MadsRudolph/Oscilloscope_Project/docs/Kicad/Spice_Models/TLV3501/TLV3501-PSpiceFiles/SCHEMATIC1/TLV3501_SIM/TLV3501_SIM.cir

** Profile: "SCHEMATIC1-TLV3501_SIM"  [ C:\Modeling\TLV3501\PSPICE\TLV3501-PSpiceFiles\SCHEMATIC1\TLV3501_SIM.sim ] 

** Creating circuit file "TLV3501_SIM.cir" 
** WARNING: THIS AUTOMATICALLY GENERATED FILE MAY BE OVERWRITTEN BY SUBSEQUENT SIMULATIONS

*Libraries: 
* Profile Libraries :
* Local Libraries :
.LIB "../../../tlv3501.lib" 
* From [PSPICE NETLIST] section of C:\SPB_DATA\cdssetup\OrCAD_PSpice\17.4.0\PSpice.ini file:
.lib "nom.lib" 

*Analysis directives: 
.TRAN  0 500ns 0 
.OPTIONS ADVCONV
.PROBE64 V(alias(*)) I(alias(*)) W(alias(*)) D(alias(*)) NOISE(alias(*)) 
.INC "..\SCHEMATIC1.net" 


.END
