MadsRudolph/Oscilloscope_Project/docs/LTspice/Projekt Filter Simulation.asc

C1: cap; 3.18n
C2: cap; 0.47n
C3: cap; 0.47n
C4: cap; 0.47n
C5: cap; 0.47n
R1: res; 6.49k
R2: res; 1000
R3: res; 6.49k
R4: res; 6.49k
R5: res; 6.49k
R6: res
U1: LT1713
U2: LT1013
U4: LT1013
V1: voltage; 5
V2: voltage; 3.3
V3: voltage; SINE(1 1 1000); AC 1 0
V4: voltage; -5
V5: voltage; 5
V6: voltage; -5
V_const: voltage; 1.65
V_saw: voltage; PULSE(0 3.3 0 0.0001 0 0 0.0001)
V_sin: voltage; SINE(1.65 1.65 1000)
V_Square: voltage; PULSE(0 3.3 0 0 0 0.0005 0.001)
V_tri: voltage; PULSE(0 3.3 0 1.28u 1.28u 0 0)
Named nets: V_tri, 0, V_Saw, PWM, V_Sin, V_Square, V_const, BODE
.tran 10m
