MadsRudolph/Oscilloscope_Project/docs/LTspice/Filter.asc

R1: res; 5
R2: res; 5
R3: res; 10
V1: voltage; 5
.tran 10
