MadsRudolph/Oscilloscope_Project/docs/Kicad/FilterDesign/Active_Filter.kicad_sch

## KiCad design docs/Kicad/FilterDesign/Active_Filter.kicad_sch (2025-06-14)

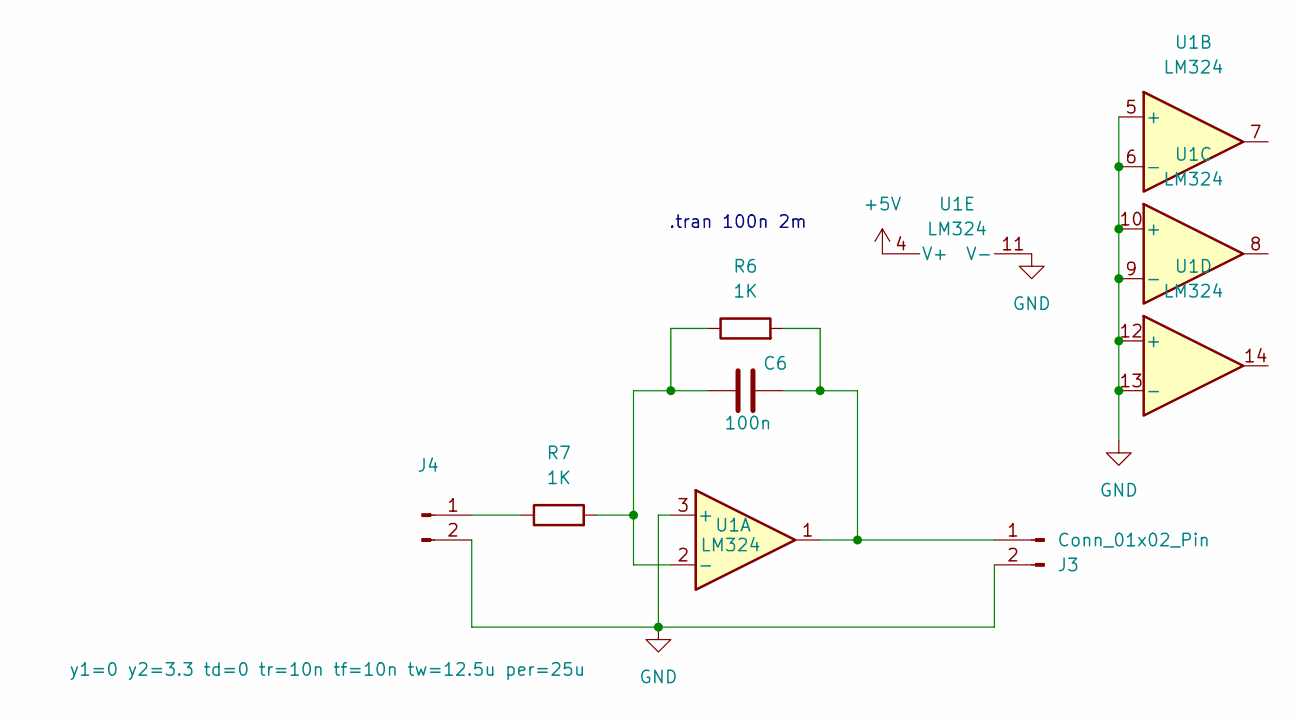
[picture p2: schematic Active_Filter.kicad_sch]

Parts:
C6: 100n
J3: Conn_01x02_Pin
J4: y1=0 y2=3.3 td=0 tr=10n tf=10n tw=12.5u per=25u
R6, R7: 1K
U1: LM324

Connections:
+5V: U1.4 (V+)
GND: J3.2, J4.2, U1.3 (+), U1.5 (+), U1.6 (-), U1.9 (-), U1.10 (+), U1.11 (V-), U1.12 (+), U1.13 (-)
unnamed: C6.1, R6.1, R7.2, U1.2 (-)
unnamed: C6.2, J3.1, R6.2, U1.1
unnamed: J4.1, R7.1

Notes on the sheet:
.tran 100n 2m
