MadsRudolph/Oscilloscope_Project/docs/Kicad/FilterDesign/Passive_filter.kicad_sch

## KiCad design docs/Kicad/FilterDesign/Passive_filter.kicad_sch (2025-06-16, an earlier design)

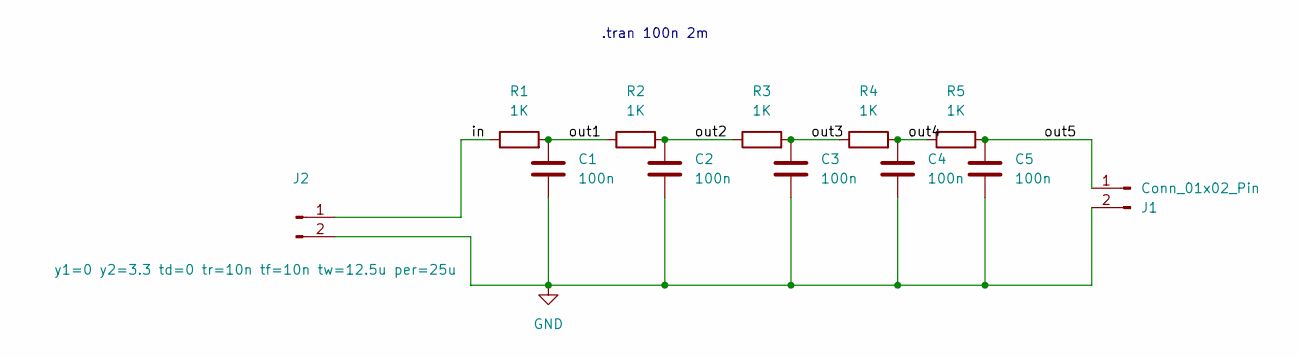
[picture p3: schematic Passive_filter.kicad_sch]

Parts:
C1, C2, C3, C4, C5: 100n
J1: Conn_01x02_Pin
J2: y1=0 y2=3.3 td=0 tr=10n tf=10n tw=12.5u per=25u
R1, R2, R3, R4, R5: 1K

Connections:
GND: C1.2, C2.2, C3.2, C4.2, C5.2, J1.2, J2.2
in: J2.1, R1.1
out1: C1.1, R1.2, R2.1
out2: C2.1, R2.2, R3.1
out3: C3.1, R3.2, R4.1
out4: C4.1, R4.2, R5.1
out5: C5.1, J1.1, R5.2

Notes on the sheet:
.tran 100n 2m
