MadsRudolph/Oscilloscope_Project/docs/Kicad/FilterDesign/Sallen-key topology low-pass.kicad_sch

## KiCad design docs/Kicad/FilterDesign/Sallen-key topology low-pass.kicad_sch (2025-06-19, an earlier design)

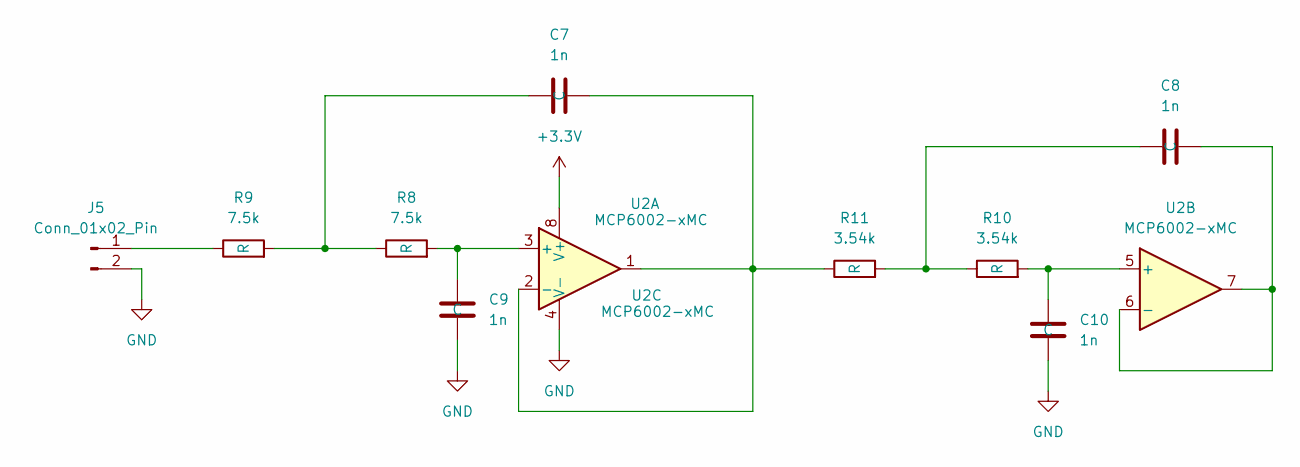
[picture p4: schematic Sallen-key topology low-pass.kicad_sch]

Parts:
C7, C8, C9, C10: 1n
J5: Conn_01x02_Pin
R8, R9: 7.5k
R10, R11: 3.54k
U2: MCP6002-xMC; DFN-8-1EP_3x2mm_P0.5mm_EP1.75x1.45mm

Connections:
+3.3V: U2.8 (V+)
GND: C9.2, C10.2, J5.2, U2.4 (V-), U2.9 (V-)
unnamed: C7.1, R8.1, R9.2
unnamed: C7.2, R11.1, U2.1, U2.2 (-)
unnamed: C8.1, R10.1, R11.2
unnamed: C8.2, U2.6 (-), U2.7
unnamed: C9.1, R8.2, U2.3 (+)
unnamed: C10.1, R10.2, U2.5 (+)
unnamed: J5.1, R9.1
