MadsRudolph/Oscilloscope_Project/docs/Kicad/FilterDesign/AktivtFilterSim/AktivtFilterSim.kicad_sch

## KiCad design docs/Kicad/FilterDesign/AktivtFilterSim/AktivtFilterSim.kicad_sch (2025-06-19, an earlier design)

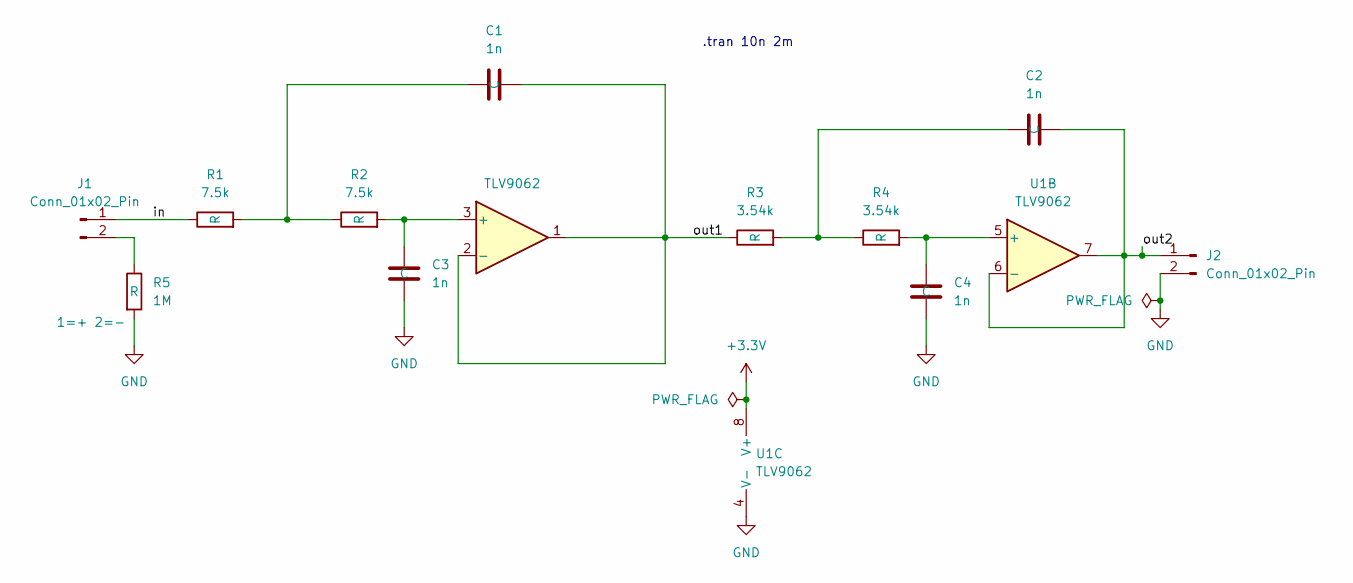
[picture p5: schematic AktivtFilterSim.kicad_sch]

Parts:
C1, C2, C3, C4: 1n
J1, J2: Conn_01x02_Pin
R1, R2: 7.5k
R3, R4: 3.54k
R5: 1M
U1: TLV9062

Connections:
+3.3V: U1.8 (V+)
GND: C3.2, C4.2, J2.2, R5.2, U1.4 (V-)
unnamed: C1.1, R1.2, R2.1
unnamed: C2.1, R3.2, R4.1
unnamed: C3.1, R2.2, U1.3 (+)
unnamed: C4.1, R4.2, U1.5 (+)
unnamed: J1.2, R5.1
in: J1.1, R1.1
out1: C1.2, R3.1, U1.1, U1.2 (-)
out2: C2.2, J2.1, U1.6 (-), U1.7

Notes on the sheet:
.tran 10n 2m
