MadsRudolph/Oscilloscope_Project/docs/Kicad/FilterDesign/Comparator/Comparator.kicad_sch

## KiCad design docs/Kicad/FilterDesign/Comparator/Comparator.kicad_sch (2025-06-19)

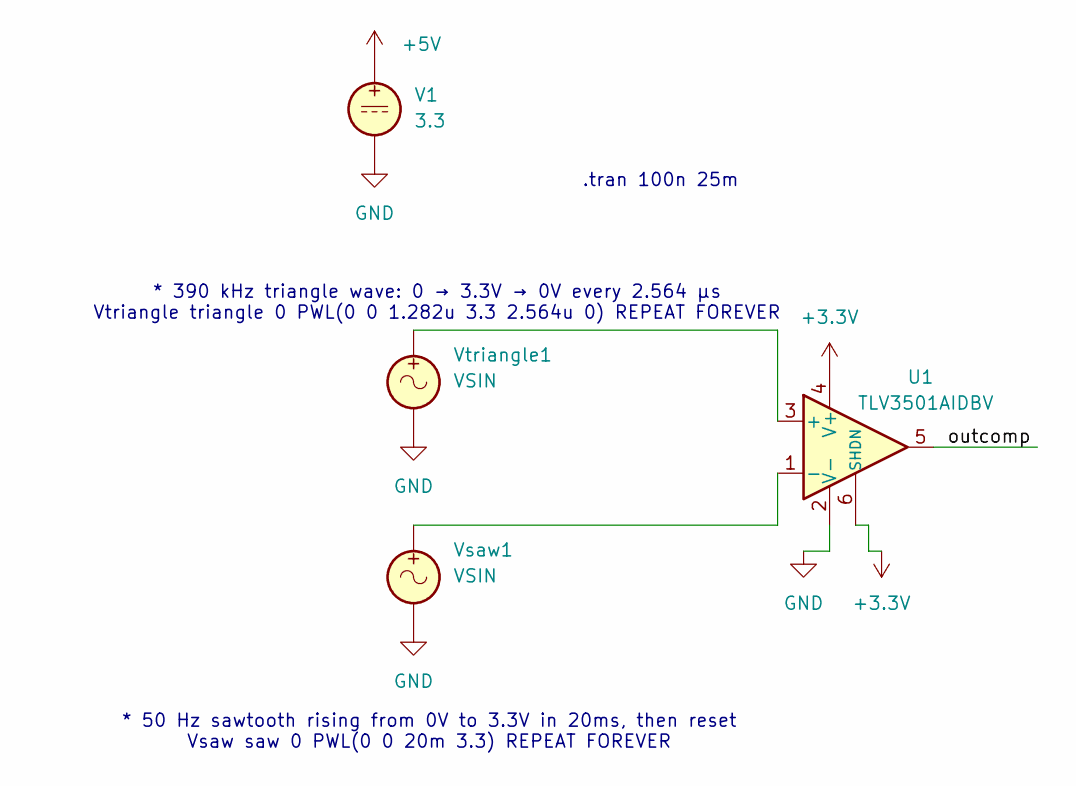
[picture p6: schematic Comparator.kicad_sch]

Parts:
U1: TLV3501AIDBV; SOT-23-6
V1: 3.3
Vsaw1: VSIN
Vtriangle1: VSIN

Connections:
+3.3V: U1.4 (V+), U1.6 (SHDN)
+5V: V1.1
GND: U1.2 (V-), V1.2, Vsaw1.2, Vtriangle1.2
unnamed: U1.1 (-), Vsaw1.1
unnamed: U1.3 (+), Vtriangle1.1
outcomp: U1.5

Notes on the sheet:
.tran 100n 25m
* 390 kHz triangle wave: 0 → 3.3V → 0V every 2.564 µs Vtriangle triangle 0 PWL(0 0 1.282u 3.3 2.564u 0) REPEAT FOREVER
* 50 Hz sawtooth rising from 0V to 3.3V in 20ms, then reset Vsaw saw 0 PWL(0 0 20m 3.3) REPEAT FOREVER
