MadsRudolph/Oscilloscope_Project/docs/Kicad/FilterDesign/FinalFilter/FinalFilter.kicad_sch

## KiCad design docs/Kicad/FilterDesign/FinalFilter/FinalFilter.kicad_sch (2025-06-23)

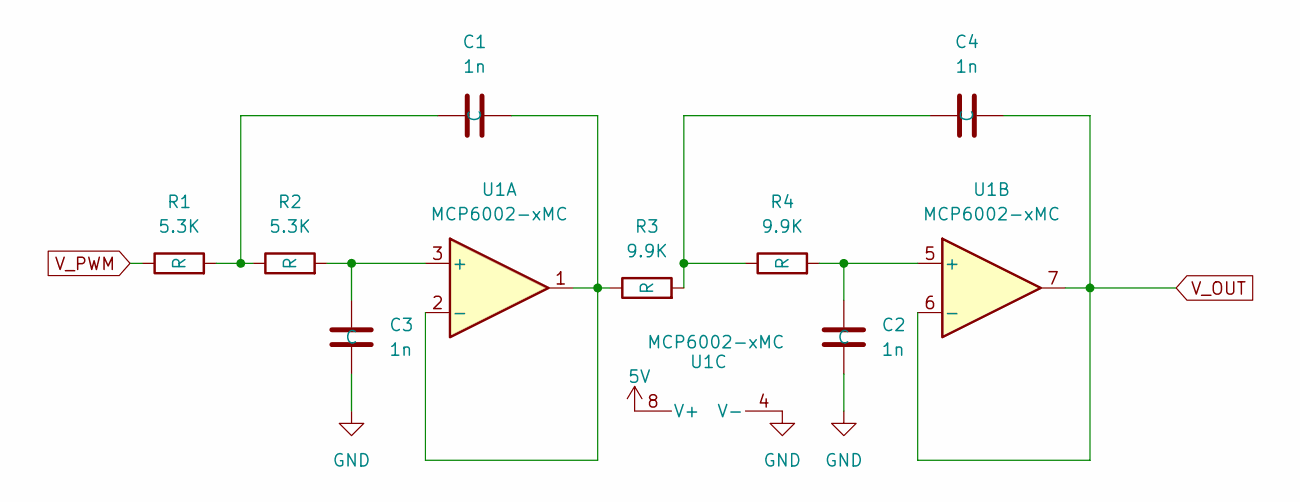
[picture p7: schematic FinalFilter.kicad_sch]

Parts:
C1, C2, C3, C4: 1n
R1, R2: 5.3K
R3, R4: 9.9K
U1: MCP6002-xMC; DFN-8-1EP_3x2mm_P0.5mm_EP1.75x1.45mm

Connections:
5V: U1.8 (V+)
GND: C2.2, C3.2, U1.4 (V-), U1.9 (V-)
unnamed: C1.1, R1.2, R2.1
unnamed: C1.2, R3.1, U1.1, U1.2 (-)
unnamed: C2.1, R4.2, U1.5 (+)
unnamed: C3.1, R2.2, U1.3 (+)
unnamed: C4.1, R3.2, R4.1
V_OUT: C4.2, U1.6 (-), U1.7
V_PWM: R1.1
