MadsRudolph/Oscilloscope_Project/fpga/SPI_Test/ProtokolBlok.vhd

library IEEE;
use IEEE.STD_LOGIC_1164.ALL;
use IEEE.STD_LOGIC_UNSIGNED.ALL;


entity ProtokolBlok is
    Port ( CLK : in STD_LOGIC;
			  Reset : in STD_LOGIC;
			  DataReady : in STD_LOGIC;
			  SPIdat: in STD_LOGIC_VECTOR (7 downto 0);
			  Shape: out STD_LOGIC_VECTOR (2 downto 0);
			  Amp: out STD_LOGIC_VECTOR (7 downto 0);
			  LD: out STD_LOGIC;
			  LD2: out STD_LOGIC;
			  LD3: out STD_LOGIC;
			  LD4: out STD_LOGIC;
			  Freq: out STD_LOGIC_VECTOR (7 downto 0);
			  SigEN: inout STD_LOGIC);
end ProtokolBlok;

architecture Behavioral of ProtokolBlok is

type Statetype is (IDLE, ADDRS, DataS, CheckSumEnS, CheckSumS, AmpS, ShapeS, FreqS);

signal state, nextstate : Statetype;
signal DataEN, ADDREN, AmpEN, FreqEN, ShapeEN, ShapeEN_prev, CheckSumEN, Chk, syncbyte, SigENEN, UnderFlag, OverFlag, LigeFlag: STD_LOGIC;
signal CheckSum, ADDR, Data: STD_LOGIC_VECTOR (7 downto 0);
signal TestCnt: STD_LOGIC_VECTOR(15 downto 0):= "0000000000000000"; -- Dette er til test af robust kommunikation

begin


SyncDec: syncbyte <= '1' when SPIdat = "01010101" else '0'; --Byte som indikerer start af datapakke

CheckSumDec: Chk <= '1' when Checksum = (("01010101" xor ADDR) xor Data) else '0'; -- Kontrol signal som indikere at data er modtaget korrekt

Statereg: process(CLK, Reset)
    begin 
        if Reset = '1' then 
            state <= IDLE;  -- Reset state to IDLE
				TestCnt <= "0000000000000000";
		  elsif CLK'event and CLK = '1' then
            state <= nextstate;  -- Update state on clock edge
				if ShapeEN = '1' and ShapeEN_prev = '0' then -- puls som sikrer vi tller en op p antal shapes modtaget korrekt
					TestCnt <= TestCnt + "0000000000000001"; -- Tæller til robusthed
				end if; 
				ShapeEN_prev <= ShapeEN;
			
        end if;
    end process;

    -- Next state logic and register enable control
    StateDec: process (DataReady, state, Chk, syncbyte, ADDR)
    begin
	 	 
-- Default values
	DataEn <= '0';
	ADDREn <= '0';
	CheckSumEn <= '0';
	AmpEn <= '0';
	ShapeEn <= '0';
	FreqEn <= '0';
	SigENEN <= '0';
	
	--State machine
	
	case state is
	
	when IDLE =>
		if syncbyte  = '1' and DataReady = '1' then  -- check spidat(sync) stemmer
			SigENEN <='0';
			nextstate <= ADDRS;
		else
			nextstate <= IDLE;
		end if; 
	
	when ADDRS =>
		if DataReady = '1' then
			ADDREN <= '1';
			nextstate <= DataS;
		else
			nextstate <= ADDRS;
		end if;
	
	
	when DataS =>
		if DataReady = '1' then
			DataEN <= '1';
			nextstate <= CheckSumEnS;
		else
			nextstate <= DataS;
		end if;
		
   when CheckSumEnS =>
		if DataReady = '1' then
			CheckSumEn <= '1';
			nextstate <= CheckSumS;
		else
			nextstate <= CheckSumEnS;
		end if;

	when CheckSumS => -- Styring af hvilken data, der skal indlæses
		if Chk = '1' and ADDR = "00000001" then
			nextstate <= AmpS;
			
		elsif Chk = '1' and ADDR = "00000010" then
			nextstate <= FreqS;
		elsif Chk = '1' and ADDR = "00000011" then
			nextstate <= ShapeS;
		else
			nextstate <=IDLE;			
		end if;
		

	when AmpS =>
			AmpEN <= '1';
			nextstate <= IDLE;

	
	when FreqS =>
			FreqEN <= '1';
			nextstate <= IDLE;

			
	when ShapeS =>
			ShapeEN <= '1';
			SigENEN <= '1'; -- Enable signal til Signalenable
			nextstate <= IDLE;
end case;


end process;


Process(TestCnt) -- Kontrol af kommunikations robusthed.
begin
	if TestCnt < "0010101001001011" then -- led lys hvis under 10827 shapes
	UnderFlag <= '1';
	OverFlag <= '0';
	LigeFlag <= '0'; 
	elsif TestCnt = "0010101001001011" then -- led lyser hvis over 10827 shapes
	OverFlag <= '0';
	UnderFlag <= '0';
	LigeFlag <= '1';
	elsif TestCnt > "0010101001001011" then -- led lyser hvis over 10827 shapes
	OverFlag <= '1';
	LigeFlag <= '0';
	UnderFlag <= '0';
	else 
		UnderFlag <= '0'; 
		OverFlag <= '0';
		LigeFlag <= '0'; 
	end if; 
end process; 

LD <= SigEn;
LD2 <= UnderFlag;
LD3 <= OverFlag; 
LD4 <= LigeFlag; 
ADDRReg: entity work.std_8bit_reg
	port map (
					Reset => Reset,
					Clk => Clk,
					Enable => ADDREn,
					Data_in => SPIdat,
					Data_out => ADDR
					);
					
DataReg: entity work.std_8bit_reg
	port map (
					Reset => Reset,
					Clk => Clk,
					Enable => DataEN,
					Data_in => SPIdat,
					Data_out => Data 
					);

CheckSumReg: entity work.std_8bit_reg
	port map (
					Reset => Reset,
					Clk => Clk,
					Enable => CheckSumEn,
					Data_in => SPIdat,
					Data_out => CheckSum 
					);



ShapeReg: entity work.std_3bit_reg
	port map (
					Reset => Reset,
					Clk => Clk,
					Enable => ShapeEn,
					Data_in => Data (2 downto 0),
					Data_out => Shape 
					);


AmpReg: entity work.std_8bit_reg
	port map (
					Reset => Reset,
					Clk => Clk,
					Enable => AmpEn,
					Data_in => Data,
					Data_out => Amp 
					);


FreqReg: entity work.std_8bit_reg
	port map (
					Reset => Reset,
					Clk => Clk,
					Enable => FreqEn,
					Data_in => Data,
					Data_out => Freq
					);

SigENReg : entity work.std_1bit_reg
	port map (
					Reset => Reset,
					Clk => Clk,
					Enable => SigENEN,
					Data_in => SigENEN,
					Data_out => SigEN
					);

end Behavioral;
